viktor-nikolov/MicroZed-carrier-board/board_demo_hw_and_sw/board_demo_MicroZed_7010_Vitis_workspace/system/ps7_cortexa9_0/standalone_domain/bsp/ps7_cortexa9_0/include/xparameters.h

#ifndef XPARAMETERS_H   /* prevent circular inclusions */
#define XPARAMETERS_H   /* by using protection macros */

/* Definition for CPU ID */
#define XPAR_CPU_ID 0U

/* Definitions for peripheral PS7_CORTEXA9_0 */
#define XPAR_PS7_CORTEXA9_0_CPU_CLK_FREQ_HZ 666666687


/******************************************************************/

/* Canonical definitions for peripheral PS7_CORTEXA9_0 */
#define XPAR_CPU_CORTEXA9_0_CPU_CLK_FREQ_HZ 666666687


/******************************************************************/

#include "xparameters_ps.h"

#define STDIN_BASEADDRESS 0xE0001000
#define STDOUT_BASEADDRESS 0xE0001000

/******************************************************************/

/* Platform specific definitions */
#define PLATFORM_ZYNQ
 
/* Definitions for sleep timer configuration */
#define XSLEEP_TIMER_IS_DEFAULT_TIMER
 
 
/******************************************************************/

/* Definitions for peripheral PS7_DDR_0 */
#define XPAR_PS7_DDR_0_S_AXI_BASEADDR 0x00100000
#define XPAR_PS7_DDR_0_S_AXI_HIGHADDR 0x3FFFFFFF


/******************************************************************/

/* Definitions for driver DEVCFG */
#define XPAR_XDCFG_NUM_INSTANCES 1U

/* Definitions for peripheral PS7_DEV_CFG_0 */
#define XPAR_PS7_DEV_CFG_0_DEVICE_ID 0U
#define XPAR_PS7_DEV_CFG_0_BASEADDR 0xF8007000U
#define XPAR_PS7_DEV_CFG_0_HIGHADDR 0xF80070FFU


/******************************************************************/

/* Canonical definitions for peripheral PS7_DEV_CFG_0 */
#define XPAR_XDCFG_0_DEVICE_ID XPAR_PS7_DEV_CFG_0_DEVICE_ID
#define XPAR_XDCFG_0_BASEADDR 0xF8007000U
#define XPAR_XDCFG_0_HIGHADDR 0xF80070FFU


/******************************************************************/

/* Definitions for driver DMAPS */
#define XPAR_XDMAPS_NUM_INSTANCES 2

/* Definitions for peripheral PS7_DMA_NS */
#define XPAR_PS7_DMA_NS_DEVICE_ID 0
#define XPAR_PS7_DMA_NS_BASEADDR 0xF8004000
#define XPAR_PS7_DMA_NS_HIGHADDR 0xF8004FFF


/* Definitions for peripheral PS7_DMA_S */
#define XPAR_PS7_DMA_S_DEVICE_ID 1
#define XPAR_PS7_DMA_S_BASEADDR 0xF8003000
#define XPAR_PS7_DMA_S_HIGHADDR 0xF8003FFF


/******************************************************************/

/* Canonical definitions for peripheral PS7_DMA_NS */
#define XPAR_XDMAPS_0_DEVICE_ID XPAR_PS7_DMA_NS_DEVICE_ID
#define XPAR_XDMAPS_0_BASEADDR 0xF8004000
#define XPAR_XDMAPS_0_HIGHADDR 0xF8004FFF

/* Canonical definitions for peripheral PS7_DMA_S */
#define XPAR_XDMAPS_1_DEVICE_ID XPAR_PS7_DMA_S_DEVICE_ID
#define XPAR_XDMAPS_1_BASEADDR 0xF8003000
#define XPAR_XDMAPS_1_HIGHADDR 0xF8003FFF


/******************************************************************/

/* Definitions for driver EMACPS */
#define XPAR_XEMACPS_NUM_INSTANCES 1

/* Definitions for peripheral PS7_ETHERNET_0 */
#define XPAR_PS7_ETHERNET_0_DEVICE_ID 0
#define XPAR_PS7_ETHERNET_0_BASEADDR 0xE000B000
#define XPAR_PS7_ETHERNET_0_HIGHADDR 0xE000BFFF
#define XPAR_PS7_ETHERNET_0_ENET_CLK_FREQ_HZ 125000000
#define XPAR_PS7_ETHERNET_0_ENET_SLCR_1000MBPS_DIV0 8
#define XPAR_PS7_ETHERNET_0_ENET_SLCR_1000MBPS_DIV1 1
#define XPAR_PS7_ETHERNET_0_ENET_SLCR_100MBPS_DIV0 8
#define XPAR_PS7_ETHERNET_0_ENET_SLCR_100MBPS_DIV1 5
#define XPAR_PS7_ETHERNET_0_ENET_SLCR_10MBPS_DIV0 8
#define XPAR_PS7_ETHERNET_0_ENET_SLCR_10MBPS_DIV1 50
#define XPAR_PS7_ETHERNET_0_ENET_TSU_CLK_FREQ_HZ 0


/******************************************************************/

#define XPAR_PS7_ETHERNET_0_IS_CACHE_COHERENT 0
#define XPAR_XEMACPS_0_IS_CACHE_COHERENT 0
/* Canonical definitions for peripheral PS7_ETHERNET_0 */
#define XPAR_XEMACPS_0_DEVICE_ID XPAR_PS7_ETHERNET_0_DEVICE_ID
#define XPAR_XEMACPS_0_BASEADDR 0xE000B000
#define XPAR_XEMACPS_0_HIGHADDR 0xE000BFFF
#define XPAR_XEMACPS_0_ENET_CLK_FREQ_HZ 125000000
#define XPAR_XEMACPS_0_ENET_SLCR_1000Mbps_DIV0 8
#define XPAR_XEMACPS_0_ENET_SLCR_1000Mbps_DIV1 1
#define XPAR_XEMACPS_0_ENET_SLCR_100Mbps_DIV0 8
#define XPAR_XEMACPS_0_ENET_SLCR_100Mbps_DIV1 5
#define XPAR_XEMACPS_0_ENET_SLCR_10Mbps_DIV0 8
#define XPAR_XEMACPS_0_ENET_SLCR_10Mbps_DIV1 50
#define XPAR_XEMACPS_0_ENET_TSU_CLK_FREQ_HZ 0


/******************************************************************/


/* Peripheral Definitions for peripheral PS7_AFI_0 */
#define XPAR_PS7_AFI_0_S_AXI_BASEADDR 0xF8008000
#define XPAR_PS7_AFI_0_S_AXI_HIGHADDR 0xF8008FFF


/* Peripheral Definitions for peripheral PS7_AFI_1 */
#define XPAR_PS7_AFI_1_S_AXI_BASEADDR 0xF8009000
#define XPAR_PS7_AFI_1_S_AXI_HIGHADDR 0xF8009FFF


/* Peripheral Definitions for peripheral PS7_AFI_2 */
#define XPAR_PS7_AFI_2_S_AXI_BASEADDR 0xF800A000
#define XPAR_PS7_AFI_2_S_AXI_HIGHADDR 0xF800AFFF


/* Peripheral Definitions for peripheral PS7_AFI_3 */
#define XPAR_PS7_AFI_3_S_AXI_BASEADDR 0xF800B000
#define XPAR_PS7_AFI_3_S_AXI_HIGHADDR 0xF800BFFF


/* Peripheral Definitions for peripheral PS7_DDRC_0 */
#define XPAR_PS7_DDRC_0_S_AXI_BASEADDR 0xF8006000
#define XPAR_PS7_DDRC_0_S_AXI_HIGHADDR 0xF8006FFF


/* Peripheral Definitions for peripheral PS7_GLOBALTIMER_0 */
#define XPAR_PS7_GLOBALTIMER_0_S_AXI_BASEADDR 0xF8F00200
#define XPAR_PS7_GLOBALTIMER_0_S_AXI_HIGHADDR 0xF8F002FF


/* Peripheral Definitions for peripheral PS7_GPV_0 */
#define XPAR_PS7_GPV_0_S_AXI_BASEADDR 0xF8900000
#define XPAR_PS7_GPV_0_S_AXI_HIGHADDR 0xF89FFFFF


/* Peripheral Definitions for peripheral PS7_INTC_DIST_0 */
#define XPAR_PS7_INTC_DIST_0_S_AXI_BASEADDR 0xF8F01000
#define XPAR_PS7_INTC_DIST_0_S_AXI_HIGHADDR 0xF8F01FFF


/* Peripheral Definitions for peripheral PS7_IOP_BUS_CONFIG_0 */
#define XPAR_PS7_IOP_BUS_CONFIG_0_S_AXI_BASEADDR 0xE0200000
#define XPAR_PS7_IOP_BUS_CONFIG_0_S_AXI_HIGHADDR 0xE0200FFF


/* Peripheral Definitions for peripheral PS7_L2CACHEC_0 */
#define XPAR_PS7_L2CACHEC_0_S_AXI_BASEADDR 0xF8F02000
#define XPAR_PS7_L2CACHEC_0_S_AXI_HIGHADDR 0xF8F02FFF


/* Peripheral Definitions for peripheral PS7_OCMC_0 */
#define XPAR_PS7_OCMC_0_S_AXI_BASEADDR 0xF800C000
#define XPAR_PS7_OCMC_0_S_AXI_HIGHADDR 0xF800CFFF


/* Peripheral Definitions for peripheral PS7_PL310_0 */
#define XPAR_PS7_PL310_0_S_AXI_BASEADDR 0xF8F02000
#define XPAR_PS7_PL310_0_S_AXI_HIGHADDR 0xF8F02FFF


/* Peripheral Definitions for peripheral PS7_PMU_0 */
#define XPAR_PS7_PMU_0_S_AXI_BASEADDR 0xF8891000
#define XPAR_PS7_PMU_0_S_AXI_HIGHADDR 0xF8891FFF
#define XPAR_PS7_PMU_0_PMU1_S_AXI_BASEADDR 0xF8893000
#define XPAR_PS7_PMU_0_PMU1_S_AXI_HIGHADDR 0xF8893FFF


/* Peripheral Definitions for peripheral PS7_QSPI_LINEAR_0 */
#define XPAR_PS7_QSPI_LINEAR_0_S_AXI_BASEADDR 0xFC000000
#define XPAR_PS7_QSPI_LINEAR_0_S_AXI_HIGHADDR 0xFCFFFFFF


/* Peripheral Definitions for peripheral PS7_RAM_0 */
#define XPAR_PS7_RAM_0_S_AXI_BASEADDR 0x00000000
#define XPAR_PS7_RAM_0_S_AXI_HIGHADDR 0x0003FFFF


/* Peripheral Definitions for peripheral PS7_RAM_1 */
#define XPAR_PS7_RAM_1_S_AXI_BASEADDR 0xFFFC0000
#define XPAR_PS7_RAM_1_S_AXI_HIGHADDR 0xFFFFFFFF


/* Peripheral Definitions for peripheral PS7_SCUC_0 */
#define XPAR_PS7_SCUC_0_S_AXI_BASEADDR 0xF8F00000
#define XPAR_PS7_SCUC_0_S_AXI_HIGHADDR 0xF8F000FC


/* Peripheral Definitions for peripheral PS7_SLCR_0 */
#define XPAR_PS7_SLCR_0_S_AXI_BASEADDR 0xF8000000
#define XPAR_PS7_SLCR_0_S_AXI_HIGHADDR 0xF8000FFF


/******************************************************************/






































/******************************************************************/

/* Definitions for driver GPIOPS */
#define XPAR_XGPIOPS_NUM_INSTANCES 1

/* Definitions for peripheral PS7_GPIO_0 */
#define XPAR_PS7_GPIO_0_DEVICE_ID 0
#define XPAR_PS7_GPIO_0_BASEADDR 0xE000A000
#define XPAR_PS7_GPIO_0_HIGHADDR 0xE000AFFF


/******************************************************************/

/* Canonical definitions for peripheral PS7_GPIO_0 */
#define XPAR_XGPIOPS_0_DEVICE_ID XPAR_PS7_GPIO_0_DEVICE_ID
#define XPAR_XGPIOPS_0_BASEADDR 0xE000A000
#define XPAR_XGPIOPS_0_HIGHADDR 0xE000AFFF


/******************************************************************/

/* Definitions for driver QSPIPS */
#define XPAR_XQSPIPS_NUM_INSTANCES 1

/* Definitions for peripheral PS7_QSPI_0 */
#define XPAR_PS7_QSPI_0_DEVICE_ID 0
#define XPAR_PS7_QSPI_0_BASEADDR 0xE000D000
#define XPAR_PS7_QSPI_0_HIGHADDR 0xE000DFFF
#define XPAR_PS7_QSPI_0_QSPI_CLK_FREQ_HZ 200000000
#define XPAR_PS7_QSPI_0_QSPI_MODE 0
#define XPAR_PS7_QSPI_0_QSPI_BUS_WIDTH 2


/******************************************************************/

/* Canonical definitions for peripheral PS7_QSPI_0 */
#define XPAR_XQSPIPS_0_DEVICE_ID XPAR_PS7_QSPI_0_DEVICE_ID
#define XPAR_XQSPIPS_0_BASEADDR 0xE000D000
#define XPAR_XQSPIPS_0_HIGHADDR 0xE000DFFF
#define XPAR_XQSPIPS_0_QSPI_CLK_FREQ_HZ 200000000
#define XPAR_XQSPIPS_0_QSPI_MODE 0
#define XPAR_XQSPIPS_0_QSPI_BUS_WIDTH 2


/******************************************************************/

/* Definitions for driver SCUGIC */
#define XPAR_XSCUGIC_NUM_INSTANCES 1U

/* Definitions for peripheral PS7_SCUGIC_0 */
#define XPAR_PS7_SCUGIC_0_DEVICE_ID 0U
#define XPAR_PS7_SCUGIC_0_BASEADDR 0xF8F00100U
#define XPAR_PS7_SCUGIC_0_HIGHADDR 0xF8F001FFU
#define XPAR_PS7_SCUGIC_0_DIST_BASEADDR 0xF8F01000U


/******************************************************************/

/* Canonical definitions for peripheral PS7_SCUGIC_0 */
#define XPAR_SCUGIC_0_DEVICE_ID 0U
#define XPAR_SCUGIC_0_CPU_BASEADDR 0xF8F00100U
#define XPAR_SCUGIC_0_CPU_HIGHADDR 0xF8F001FFU
#define XPAR_SCUGIC_0_DIST_BASEADDR 0xF8F01000U


/******************************************************************/

/* Definitions for driver SCUTIMER */
#define XPAR_XSCUTIMER_NUM_INSTANCES 1

/* Definitions for peripheral PS7_SCUTIMER_0 */
#define XPAR_PS7_SCUTIMER_0_DEVICE_ID 0
#define XPAR_PS7_SCUTIMER_0_BASEADDR 0xF8F00600
#define XPAR_PS7_SCUTIMER_0_HIGHADDR 0xF8F0061F


/******************************************************************/

/* Canonical definitions for peripheral PS7_SCUTIMER_0 */
#define XPAR_XSCUTIMER_0_DEVICE_ID XPAR_PS7_SCUTIMER_0_DEVICE_ID
#define XPAR_XSCUTIMER_0_BASEADDR 0xF8F00600
#define XPAR_XSCUTIMER_0_HIGHADDR 0xF8F0061F


/******************************************************************/

/* Definitions for driver SCUWDT */
#define XPAR_XSCUWDT_NUM_INSTANCES 1

/* Definitions for peripheral PS7_SCUWDT_0 */
#define XPAR_PS7_SCUWDT_0_DEVICE_ID 0
#define XPAR_PS7_SCUWDT_0_BASEADDR 0xF8F00620
#define XPAR_PS7_SCUWDT_0_HIGHADDR 0xF8F006FF


/******************************************************************/

/* Canonical definitions for peripheral PS7_SCUWDT_0 */
#define XPAR_SCUWDT_0_DEVICE_ID XPAR_PS7_SCUWDT_0_DEVICE_ID
#define XPAR_SCUWDT_0_BASEADDR 0xF8F00620
#define XPAR_SCUWDT_0_HIGHADDR 0xF8F006FF


/******************************************************************/

/* Definitions for driver SDPS */
#define XPAR_XSDPS_NUM_INSTANCES 1

/* Definitions for peripheral PS7_SD_0 */
#define XPAR_PS7_SD_0_DEVICE_ID 0
#define XPAR_PS7_SD_0_BASEADDR 0xE0100000
#define XPAR_PS7_SD_0_HIGHADDR 0xE0100FFF
#define XPAR_PS7_SD_0_SDIO_CLK_FREQ_HZ 25000000
#define XPAR_PS7_SD_0_HAS_CD 1
#define XPAR_PS7_SD_0_HAS_WP 1
#define XPAR_PS7_SD_0_BUS_WIDTH 0
#define XPAR_PS7_SD_0_MIO_BANK 0
#define XPAR_PS7_SD_0_HAS_EMIO 0
#define XPAR_PS7_SD_0_SLOT_TYPE 0
#define XPAR_PS7_SD_0_CLK_50_SDR_ITAP_DLY 0
#define XPAR_PS7_SD_0_CLK_50_SDR_OTAP_DLY 0
#define XPAR_PS7_SD_0_CLK_50_DDR_ITAP_DLY 0
#define XPAR_PS7_SD_0_CLK_50_DDR_OTAP_DLY 0
#define XPAR_PS7_SD_0_CLK_100_SDR_OTAP_DLY 0
#define XPAR_PS7_SD_0_CLK_200_SDR_OTAP_DLY 0


/******************************************************************/

#define XPAR_PS7_SD_0_IS_CACHE_COHERENT 0
/* Canonical definitions for peripheral PS7_SD_0 */
#define XPAR_XSDPS_0_DEVICE_ID XPAR_PS7_SD_0_DEVICE_ID
#define XPAR_XSDPS_0_BASEADDR 0xE0100000
#define XPAR_XSDPS_0_HIGHADDR 0xE0100FFF
#define XPAR_XSDPS_0_SDIO_CLK_FREQ_HZ 25000000
#define XPAR_XSDPS_0_HAS_CD 1
#define XPAR_XSDPS_0_HAS_WP 1
#define XPAR_XSDPS_0_BUS_WIDTH 0
#define XPAR_XSDPS_0_MIO_BANK 0
#define XPAR_XSDPS_0_HAS_EMIO 0
#define XPAR_XSDPS_0_SLOT_TYPE 0
#define XPAR_XSDPS_0_IS_CACHE_COHERENT 0
#define XPAR_XSDPS_0_CLK_50_SDR_ITAP_DLY 0
#define XPAR_XSDPS_0_CLK_50_SDR_OTAP_DLY 0
#define XPAR_XSDPS_0_CLK_50_DDR_ITAP_DLY 0
#define XPAR_XSDPS_0_CLK_50_DDR_OTAP_DLY 0
#define XPAR_XSDPS_0_CLK_100_SDR_OTAP_DLY 0
#define XPAR_XSDPS_0_CLK_200_SDR_OTAP_DLY 0


/******************************************************************/

/* Definitions for driver TTCPS */
#define XPAR_XTTCPS_NUM_INSTANCES 3U

/* Definitions for peripheral PS7_TTC_0 */
#define XPAR_PS7_TTC_0_DEVICE_ID 0U
#define XPAR_PS7_TTC_0_BASEADDR 0XF8001000U
#define XPAR_PS7_TTC_0_TTC_CLK_FREQ_HZ 111111115U
#define XPAR_PS7_TTC_0_TTC_CLK_CLKSRC 0U
#define XPAR_PS7_TTC_1_DEVICE_ID 1U
#define XPAR_PS7_TTC_1_BASEADDR 0XF8001004U
#define XPAR_PS7_TTC_1_TTC_CLK_FREQ_HZ 111111115U
#define XPAR_PS7_TTC_1_TTC_CLK_CLKSRC 0U
#define XPAR_PS7_TTC_2_DEVICE_ID 2U
#define XPAR_PS7_TTC_2_BASEADDR 0XF8001008U
#define XPAR_PS7_TTC_2_TTC_CLK_FREQ_HZ 111111115U
#define XPAR_PS7_TTC_2_TTC_CLK_CLKSRC 0U


/******************************************************************/

/* Canonical definitions for peripheral PS7_TTC_0 */
#define XPAR_XTTCPS_0_DEVICE_ID XPAR_PS7_TTC_0_DEVICE_ID
#define XPAR_XTTCPS_0_BASEADDR 0xF8001000U
#define XPAR_XTTCPS_0_TTC_CLK_FREQ_HZ 111111115U
#define XPAR_XTTCPS_0_TTC_CLK_CLKSRC 0U

#define XPAR_XTTCPS_1_DEVICE_ID XPAR_PS7_TTC_1_DEVICE_ID
#define XPAR_XTTCPS_1_BASEADDR 0xF8001004U
#define XPAR_XTTCPS_1_TTC_CLK_FREQ_HZ 111111115U
#define XPAR_XTTCPS_1_TTC_CLK_CLKSRC 0U

#define XPAR_XTTCPS_2_DEVICE_ID XPAR_PS7_TTC_2_DEVICE_ID
#define XPAR_XTTCPS_2_BASEADDR 0xF8001008U
#define XPAR_XTTCPS_2_TTC_CLK_FREQ_HZ 111111115U
#define XPAR_XTTCPS_2_TTC_CLK_CLKSRC 0U


/******************************************************************/

/* Definitions for driver UARTPS */
#define XPAR_XUARTPS_NUM_INSTANCES 1

/* Definitions for peripheral PS7_UART_1 */
#define XPAR_PS7_UART_1_DEVICE_ID 0
#define XPAR_PS7_UART_1_BASEADDR 0xE0001000
#define XPAR_PS7_UART_1_HIGHADDR 0xE0001FFF
#define XPAR_PS7_UART_1_UART_CLK_FREQ_HZ 50000000
#define XPAR_PS7_UART_1_HAS_MODEM 0


/******************************************************************/

/* Canonical definitions for peripheral PS7_UART_1 */
#define XPAR_XUARTPS_0_DEVICE_ID XPAR_PS7_UART_1_DEVICE_ID
#define XPAR_XUARTPS_0_BASEADDR 0xE0001000
#define XPAR_XUARTPS_0_HIGHADDR 0xE0001FFF
#define XPAR_XUARTPS_0_UART_CLK_FREQ_HZ 50000000
#define XPAR_XUARTPS_0_HAS_MODEM 0


/******************************************************************/

/* Definition for input Clock */
/* Definitions for driver USBPS */
#define XPAR_XUSBPS_NUM_INSTANCES 1

/* Definitions for peripheral PS7_USB_0 */
#define XPAR_PS7_USB_0_DEVICE_ID 0
#define XPAR_PS7_USB_0_BASEADDR 0xE0002000
#define XPAR_PS7_USB_0_HIGHADDR 0xE0002FFF


/******************************************************************/

/* Canonical definitions for peripheral PS7_USB_0 */
#define XPAR_XUSBPS_0_DEVICE_ID XPAR_PS7_USB_0_DEVICE_ID
#define XPAR_XUSBPS_0_BASEADDR 0xE0002000
#define XPAR_XUSBPS_0_HIGHADDR 0xE0002FFF


/******************************************************************/

/* Definitions for driver XADCPS */
#define XPAR_XADCPS_NUM_INSTANCES 1

/* Definitions for peripheral PS7_XADC_0 */
#define XPAR_PS7_XADC_0_DEVICE_ID 0
#define XPAR_PS7_XADC_0_BASEADDR 0xF8007100
#define XPAR_PS7_XADC_0_HIGHADDR 0xF8007120


/******************************************************************/

/* Canonical definitions for peripheral PS7_XADC_0 */
#define XPAR_XADCPS_0_DEVICE_ID XPAR_PS7_XADC_0_DEVICE_ID
#define XPAR_XADCPS_0_BASEADDR 0xF8007100
#define XPAR_XADCPS_0_HIGHADDR 0xF8007120


/******************************************************************/

#endif  /* end of protection macro */
