viktor-nikolov/MicroZed-carrier-board/board_demo_hw_and_sw/board_demo_MicroZed_7010_hw/board_demo_MicroZed_7010_hw.gen/sources_1/bd/system/hdl/system_wrapper.v

//Copyright 1986-2022 Xilinx, Inc. All Rights Reserved.
//Copyright 2022-2023 Advanced Micro Devices, Inc. All Rights Reserved.
//--------------------------------------------------------------------------------
//Tool Version: Vivado v.2023.1 (win64) Build 3865809 Sun May  7 15:05:29 MDT 2023
//Date        : Sat Sep 16 17:26:04 2023
//Host        : VIKTOR-PC running 64-bit major release  (build 9200)
//Command     : generate_target system_wrapper.bd
//Design      : system_wrapper
//Purpose     : IP block netlist
//--------------------------------------------------------------------------------
`timescale 1 ps / 1 ps

module system_wrapper
   (DDR_addr,
    DDR_ba,
    DDR_cas_n,
    DDR_ck_n,
    DDR_ck_p,
    DDR_cke,
    DDR_cs_n,
    DDR_dm,
    DDR_dq,
    DDR_dqs_n,
    DDR_dqs_p,
    DDR_odt,
    DDR_ras_n,
    DDR_reset_n,
    DDR_we_n,
    FIXED_IO_ddr_vrn,
    FIXED_IO_ddr_vrp,
    FIXED_IO_mio,
    FIXED_IO_ps_clk,
    FIXED_IO_ps_porb,
    FIXED_IO_ps_srstb,
    J3_01,
    J3_02,
    J3_03,
    J3_04,
    J3_05,
    J3_06,
    J3_07,
    J3_08,
    J3_09,
    J3_10,
    J3_11,
    J3_12,
    J3_13,
    J3_14,
    J3_15,
    J3_16,
    J3_17,
    J3_18,
    J3_19,
    J3_20,
    J3_21,
    J3_22,
    J3_23,
    J3_24,
    J3_27,
    J3_28,
    J3_29,
    J3_30,
    J3_31,
    J3_33_UART_TX,
    J3_34,
    J3_35,
    J3_36,
    J3_37,
    J3_38,
    J3_39,
    J3_40,
    J3_41,
    J4_01,
    J4_02,
    J4_03,
    J4_04,
    J4_05,
    J4_06,
    J4_07,
    J4_08,
    J4_09,
    J4_10,
    J4_11,
    J4_12,
    J4_13,
    J4_14,
    J4_16,
    J4_17,
    J4_20,
    J4_21,
    J4_22,
    J4_23,
    J4_24,
    J4_25,
    J4_26,
    J4_27,
    J4_28,
    J4_29,
    J4_30,
    J4_31,
    J4_32,
    J4_33,
    LED1,
    LED2,
    OSC_50MHZ,
    PMOD1_1,
    PMOD1_2,
    PMOD1_3,
    PMOD1_4,
    PMOD1_5,
    PMOD1_6,
    PMOD1_7,
    PMOD1_8,
    PMOD2_1,
    PMOD2_2,
    PMOD2_3,
    PMOD2_4,
    PMOD2_5,
    PMOD2_6,
    PMOD2_7,
    PMOD2_8,
    PMOD3_1,
    PMOD3_2,
    PMOD3_3,
    PMOD3_4,
    PMOD3_5,
    PMOD3_6,
    PMOD3_7,
    PMOD3_8,
    SWITCH1,
    SWITCH2);
  inout [14:0]DDR_addr;
  inout [2:0]DDR_ba;
  inout DDR_cas_n;
  inout DDR_ck_n;
  inout DDR_ck_p;
  inout DDR_cke;
  inout DDR_cs_n;
  inout [3:0]DDR_dm;
  inout [31:0]DDR_dq;
  inout [3:0]DDR_dqs_n;
  inout [3:0]DDR_dqs_p;
  inout DDR_odt;
  inout DDR_ras_n;
  inout DDR_reset_n;
  inout DDR_we_n;
  inout FIXED_IO_ddr_vrn;
  inout FIXED_IO_ddr_vrp;
  inout [53:0]FIXED_IO_mio;
  inout FIXED_IO_ps_clk;
  inout FIXED_IO_ps_porb;
  inout FIXED_IO_ps_srstb;
  output J3_01;
  output [0:0]J3_02;
  output [0:0]J3_03;
  output [0:0]J3_04;
  output [0:0]J3_05;
  output [0:0]J3_06;
  output [0:0]J3_07;
  output [0:0]J3_08;
  output [0:0]J3_09;
  output [0:0]J3_10;
  output [0:0]J3_11;
  output [0:0]J3_12;
  output [0:0]J3_13;
  output [0:0]J3_14;
  output [0:0]J3_15;
  output [0:0]J3_16;
  output [0:0]J3_17;
  output [0:0]J3_18;
  output [0:0]J3_19;
  output [0:0]J3_20;
  output [0:0]J3_21;
  output [0:0]J3_22;
  output [0:0]J3_23;
  output [0:0]J3_24;
  output [0:0]J3_27;
  output [0:0]J3_28;
  output [0:0]J3_29;
  output [0:0]J3_30;
  output [0:0]J3_31;
  output J3_33_UART_TX;
  output [0:0]J3_34;
  output [0:0]J3_35;
  output [0:0]J3_36;
  output [0:0]J3_37;
  output [0:0]J3_38;
  output [0:0]J3_39;
  output [0:0]J3_40;
  output [0:0]J3_41;
  output [0:0]J4_01;
  output [0:0]J4_02;
  output [0:0]J4_03;
  output [0:0]J4_04;
  output [0:0]J4_05;
  output [0:0]J4_06;
  output [0:0]J4_07;
  output [0:0]J4_08;
  output [0:0]J4_09;
  output [0:0]J4_10;
  output [0:0]J4_11;
  output [0:0]J4_12;
  output [0:0]J4_13;
  output [0:0]J4_14;
  output [0:0]J4_16;
  output [0:0]J4_17;
  output [0:0]J4_20;
  output [0:0]J4_21;
  output [0:0]J4_22;
  output [0:0]J4_23;
  output [0:0]J4_24;
  output [0:0]J4_25;
  output [0:0]J4_26;
  output [0:0]J4_27;
  output [0:0]J4_28;
  output [0:0]J4_29;
  output [0:0]J4_30;
  output [0:0]J4_31;
  output [0:0]J4_32;
  output [0:0]J4_33;
  output [0:0]LED1;
  output [0:0]LED2;
  input OSC_50MHZ;
  output [0:0]PMOD1_1;
  output [0:0]PMOD1_2;
  output [0:0]PMOD1_3;
  output [0:0]PMOD1_4;
  output [0:0]PMOD1_5;
  output [0:0]PMOD1_6;
  output [0:0]PMOD1_7;
  output [0:0]PMOD1_8;
  output [0:0]PMOD2_1;
  output [0:0]PMOD2_2;
  output [0:0]PMOD2_3;
  output [0:0]PMOD2_4;
  output [0:0]PMOD2_5;
  output [0:0]PMOD2_6;
  output [0:0]PMOD2_7;
  output [0:0]PMOD2_8;
  output [0:0]PMOD3_1;
  output [0:0]PMOD3_2;
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
        .PMOD2_5(PMOD2_5),
        .PMOD2_6(PMOD2_6),
        .PMOD2_7(PMOD2_7),
        .PMOD2_8(PMOD2_8),
        .PMOD3_1(PMOD3_1),
        .PMOD3_2(PMOD3_2),
        .PMOD3_3(PMOD3_3),
        .PMOD3_4(PMOD3_4),
        .PMOD3_5(PMOD3_5),
        .PMOD3_6(PMOD3_6),
        .PMOD3_7(PMOD3_7),
        .PMOD3_8(PMOD3_8),
        .SWITCH1(SWITCH1),
        .SWITCH2(SWITCH2));
endmodule
